camistrate/InkTime_Project/Hardware/schematic.sch

## EAGLE design Hardware/schematic.sch (2026-04-10)

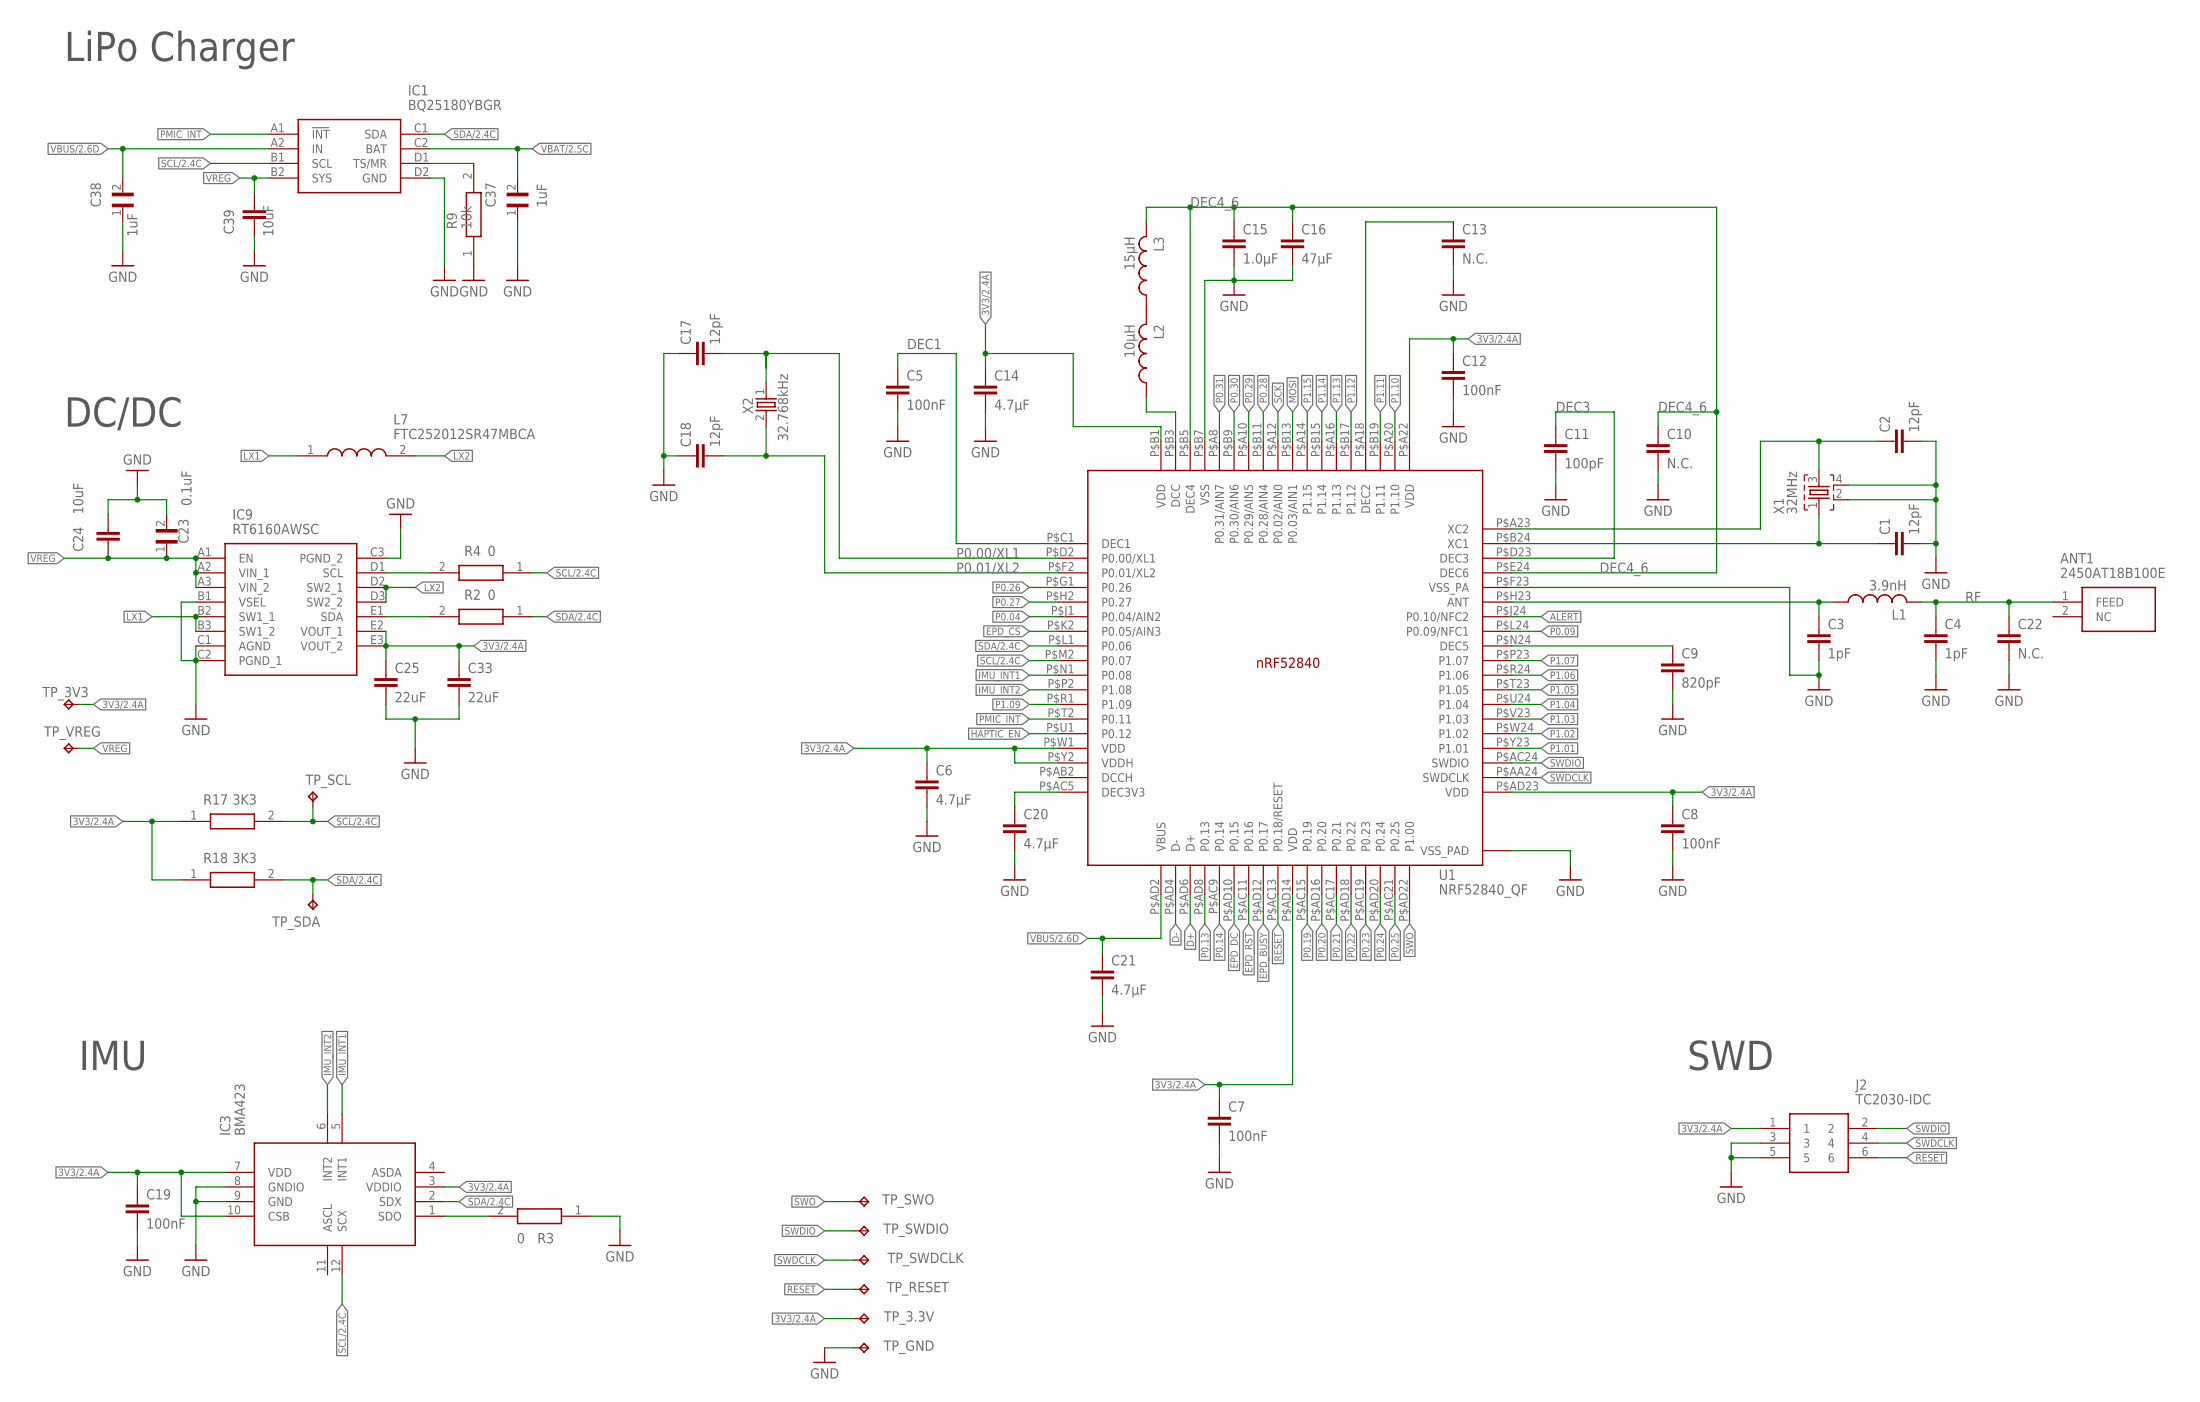
[picture p7: schematic schematic.sch, sheet 1]

Parts:
ANT1: 2450AT18B100E; 2450AT18B100E_ANTC3216X140N
C1, C2, C17, C18: 12pF; NORDIC_NRF_3_RESC0201_L
C3, C4: 1pF; NORDIC_NRF_3_RESC0201_L
C5, C7, C8, C12, C19: 100nF; NORDIC_NRF_3_RESC0201_L
C6, C14, C20, C21: 4.7µF; NORDIC_NRF_3_RESC0402_L
C9: 820pF; NORDIC_NRF_3_RESC0201_L
C10, C13, C22: N.C.; NORDIC_NRF_3_RESC0201_L
C11: 100pF; NORDIC_NRF_3_RESC0201_L
C15: 1.0µF; NORDIC_NRF_3_RESC0402_L
C16: 47µF; NORDIC_NRF_3_RESC0402_L
C23: 0.1uF; GRM011R60J152KE01L_2_CAPC0201X13N
C24, C39: 10uF; NORDIC_NRF_3_RESC0402_L
C25, C33: 22uF; NORDIC_NRF_3_RESC0402_L
C37, C38: 1uF; GRM011R60J152KE01L_2_CAPC0201X13N
IC1: BQ25180YBGR; BQ25180YBGR_BGA8C40P2X4_100X155X50
IC3: BMA423; BMA423_BMA423
IC9: RT6160AWSC; RT6160AWSC_BGA15C40P3X5_140X230X60
J2: TC2030-IDC; TC2030-IDC_TC2030IDC
L1: 3.9nH; NORDIC_NRF_2_RESC0201_N
L2: 10µH; NORDIC_NRF_2_RESC0201_N
L3: 15µH; NORDIC_NRF_2_RESC0201_N
L7: FTC252012SR47MBCA; MLP2016SR47MT0S1_INDC2016X100N
R2, R4: 0; CPF0201D7K68C1_0201
R3: 0; ERA-1AEB3401C_0201
R9: 10k; CPF0201D7K68C1_0201
R17, R18: 3K3; ERA-1AEB3401C_0201
TP_3.3V, TP_3V3: HECTOR_WATCH_1_TPTP20R; HECTOR_WATCH_1_TP20R
TP_GND: HECTOR_WATCH_1_TPTP20R; HECTOR_WATCH_1_TP20R
TP_RESET: HECTOR_WATCH_1_TPTP20R; HECTOR_WATCH_1_TP20R
TP_SCL: HECTOR_WATCH_1_TPTP20R; HECTOR_WATCH_1_TP20R
TP_SDA: HECTOR_WATCH_1_TPTP20R; HECTOR_WATCH_1_TP20R
TP_SWDCLK: HECTOR_WATCH_1_TPTP20R; HECTOR_WATCH_1_TP20R
TP_SWDIO: HECTOR_WATCH_1_TPTP20R; HECTOR_WATCH_1_TP20R
TP_SWO: HECTOR_WATCH_1_TPTP20R; HECTOR_WATCH_1_TP20R
TP_VREG: HECTOR_WATCH_1_TPTP20R; HECTOR_WATCH_1_TP20R
U1: NRF52840_QF; NORDIC_NRF_4_AQFN50P700X700X85_HS-74N
X1: 32MHz; NORDIC_NRF_BT-XTAL_2016_N
X2: 32.768kHz; NORDIC_NRF_1_XTAL_3215_N

Connections:
3V3/2.4A: C6.1, C7.1, C8.1, C12.1, C14.1, C19.1, C25.1, C33.1, IC3.3 (VDDIO), IC3.7 (VDD), IC3.10 (CSB), IC9.E2 (VOUT_1), IC9.E3 (VOUT_2), J2.1, R17.1, R18.1, TP_3.3V.TP, TP_3V3.TP, U1.P$A22 (VDD), U1.P$AD14 (VDD), U1.P$AD23 (VDD), U1.P$B1 (VDD), U1.P$W1 (VDD), U1.P$Y2 (VDDH)
ALERT: U1.P$J24 (P0.10/NFC2)
D+: U1.P$AD6 (D+)
D-: U1.P$AD4 (D-)
DEC1: C5.1, U1.P$C1 (DEC1)
DEC3: C11.1, U1.P$D23 (DEC3)
DEC4_6: C10.1, C15.1, C16.1, L3.2, U1.P$B5 (DEC4), U1.P$E24 (DEC6)
EPD_BUSY: U1.P$AD12 (P0.17)
EPD_CS: U1.P$K2 (P0.05/AIN3)
EPD_DC: U1.P$AD10 (P0.15)
EPD_RST: U1.P$AC11 (P0.16)
GND: C1.2, C2.2, C3.2, C4.2, C5.2, C6.2, C7.2, C8.2, C9.2, C10.2, C11.2, C12.2, C13.2, C14.2, C15.2, C16.2, C17.1, C18.1, C19.2, C20.2, C21.2, C22.2, C23.2, C24.1, C25.2, C33.2, C37.1, C38.1, C39.2, IC1.D2 (GND), IC3.8 (GNDIO), IC3.9 (GND), IC9.B1 (VSEL), IC9.C1 (AGND), IC9.C2 (PGND_1), IC9.C3 (PGND_2), J2.3, J2.5, R3.1, R9.1, TP_GND.TP, U1.P$74 (VSS_PAD), U1.P$B7 (VSS), U1.P$F23 (VSS_PA), X1.2, X1.4
HAPTIC_EN: U1.P$U1 (P0.12)
IMU_INT1: IC3.5 (INT1), U1.P$N1 (P0.08)
IMU_INT2: IC3.6 (INT2), U1.P$P2 (P1.08)
LX1: IC9.B2 (SW1_1), IC9.B3 (SW1_2), L7.1
LX2: IC9.D2 (SW2_1), IC9.D3 (SW2_2), L7.2
MOSI: U1.P$B13 (P0.03/AIN1)
unnamed: IC9.D1 (SCL), R4.2
unnamed: IC1.D1 (TS/MR), R9.2
unnamed: C20.1, U1.P$AC5 (DEC3V3)
unnamed: IC9.E1 (SDA), R2.2
unnamed: IC3.1 (SDO), R3.2
unnamed: L2.1, U1.P$B3 (DCC)
unnamed: L2.2, L3.1
unnamed: C13.1, U1.P$A18 (DEC2)
unnamed: C9.1, U1.P$N24 (DEC5)
unnamed: C2.1, U1.P$A23 (XC2), X1.3
unnamed: C3.1, L1.1, U1.P$H23 (ANT)
unnamed: C1.1, U1.P$B24 (XC1), X1.1
P0.00/XL1: C17.2, U1.P$D2 (P0.00/XL1), X2.1
P0.01/XL2: C18.2, U1.P$F2 (P0.01/XL2), X2.2
P0.04: U1.P$J1 (P0.04/AIN2)
P0.09: U1.P$L24 (P0.09/NFC1)
P0.13: U1.P$AD8 (P0.13)
P0.14: U1.P$AC9 (P0.14)
P0.19: U1.P$AC15 (P0.19)
P0.20: U1.P$AD16 (P0.20)
P0.21: U1.P$AC17 (P0.21)
P0.22: U1.P$AD18 (P0.22)
P0.23: U1.P$AC19 (P0.23)
P0.24: U1.P$AD20 (P0.24)
P0.25: U1.P$AC21 (P0.25)
P0.26: U1.P$G1 (P0.26)
P0.27: U1.P$H2 (P0.27)
P0.28: U1.P$B11 (P0.28/AIN4)
P0.29: U1.P$A10 (P0.29/AIN5)
P0.30: U1.P$B9 (P0.30/AIN6)
P0.31: U1.P$A8 (P0.31/AIN7)
P1.01: U1.P$Y23 (P1.01)
P1.02: U1.P$W24 (P1.02)
P1.03: U1.P$V23 (P1.03)
P1.04: U1.P$U24 (P1.04)
P1.05: U1.P$T23 (P1.05)
P1.06: U1.P$R24 (P1.06)
P1.07: U1.P$P23 (P1.07)
P1.09: U1.P$R1 (P1.09)
P1.10: U1.P$A20 (P1.10)
P1.11: U1.P$B19 (P1.11)
P1.12: U1.P$B17 (P1.12)
P1.13: U1.P$A16 (P1.13)
P1.14: U1.P$B15 (P1.14)
P1.15: U1.P$A14 (P1.15)
PMIC_INT: IC1.A1 (!INT), U1.P$T2 (P0.11)
RESET: J2.6, TP_RESET.TP, U1.P$AC13 (P0.18/RESET)
RF: ANT1.1 (FEED), C4.1, C22.1, L1.2
SCK: U1.P$A12 (P0.02/AIN0)
SCL/2.4C: IC1.B1 (SCL), IC3.12 (SCX), R4.1, R17.2, TP_SCL.TP, U1.P$M2 (P0.07)
SDA/2.4C: IC1.C1 (SDA), IC3.2 (SDX), R2.1, R18.2, TP_SDA.TP, U1.P$L1 (P0.06)
SWDCLK: J2.4, TP_SWDCLK.TP, U1.P$AA24 (SWDCLK)
SWDIO: J2.2, TP_SWDIO.TP, U1.P$AC24 (SWDIO)
SWO: TP_SWO.TP, U1.P$AD22 (P1.00)
VBAT/2.5C: C37.2, IC1.C2 (BAT)
VBUS/2.6D: C21.1, C38.2, IC1.A2 (IN), U1.P$AD2 (VBUS)
VREG: C23.1, C24.2, C39.1, IC1.B2 (SYS), IC9.A1 (EN), IC9.A2 (VIN_1), IC9.A3 (VIN_2), TP_VREG.TP

Notes on the sheet:
LiPo Charger
DC/DC
IMU
SWD

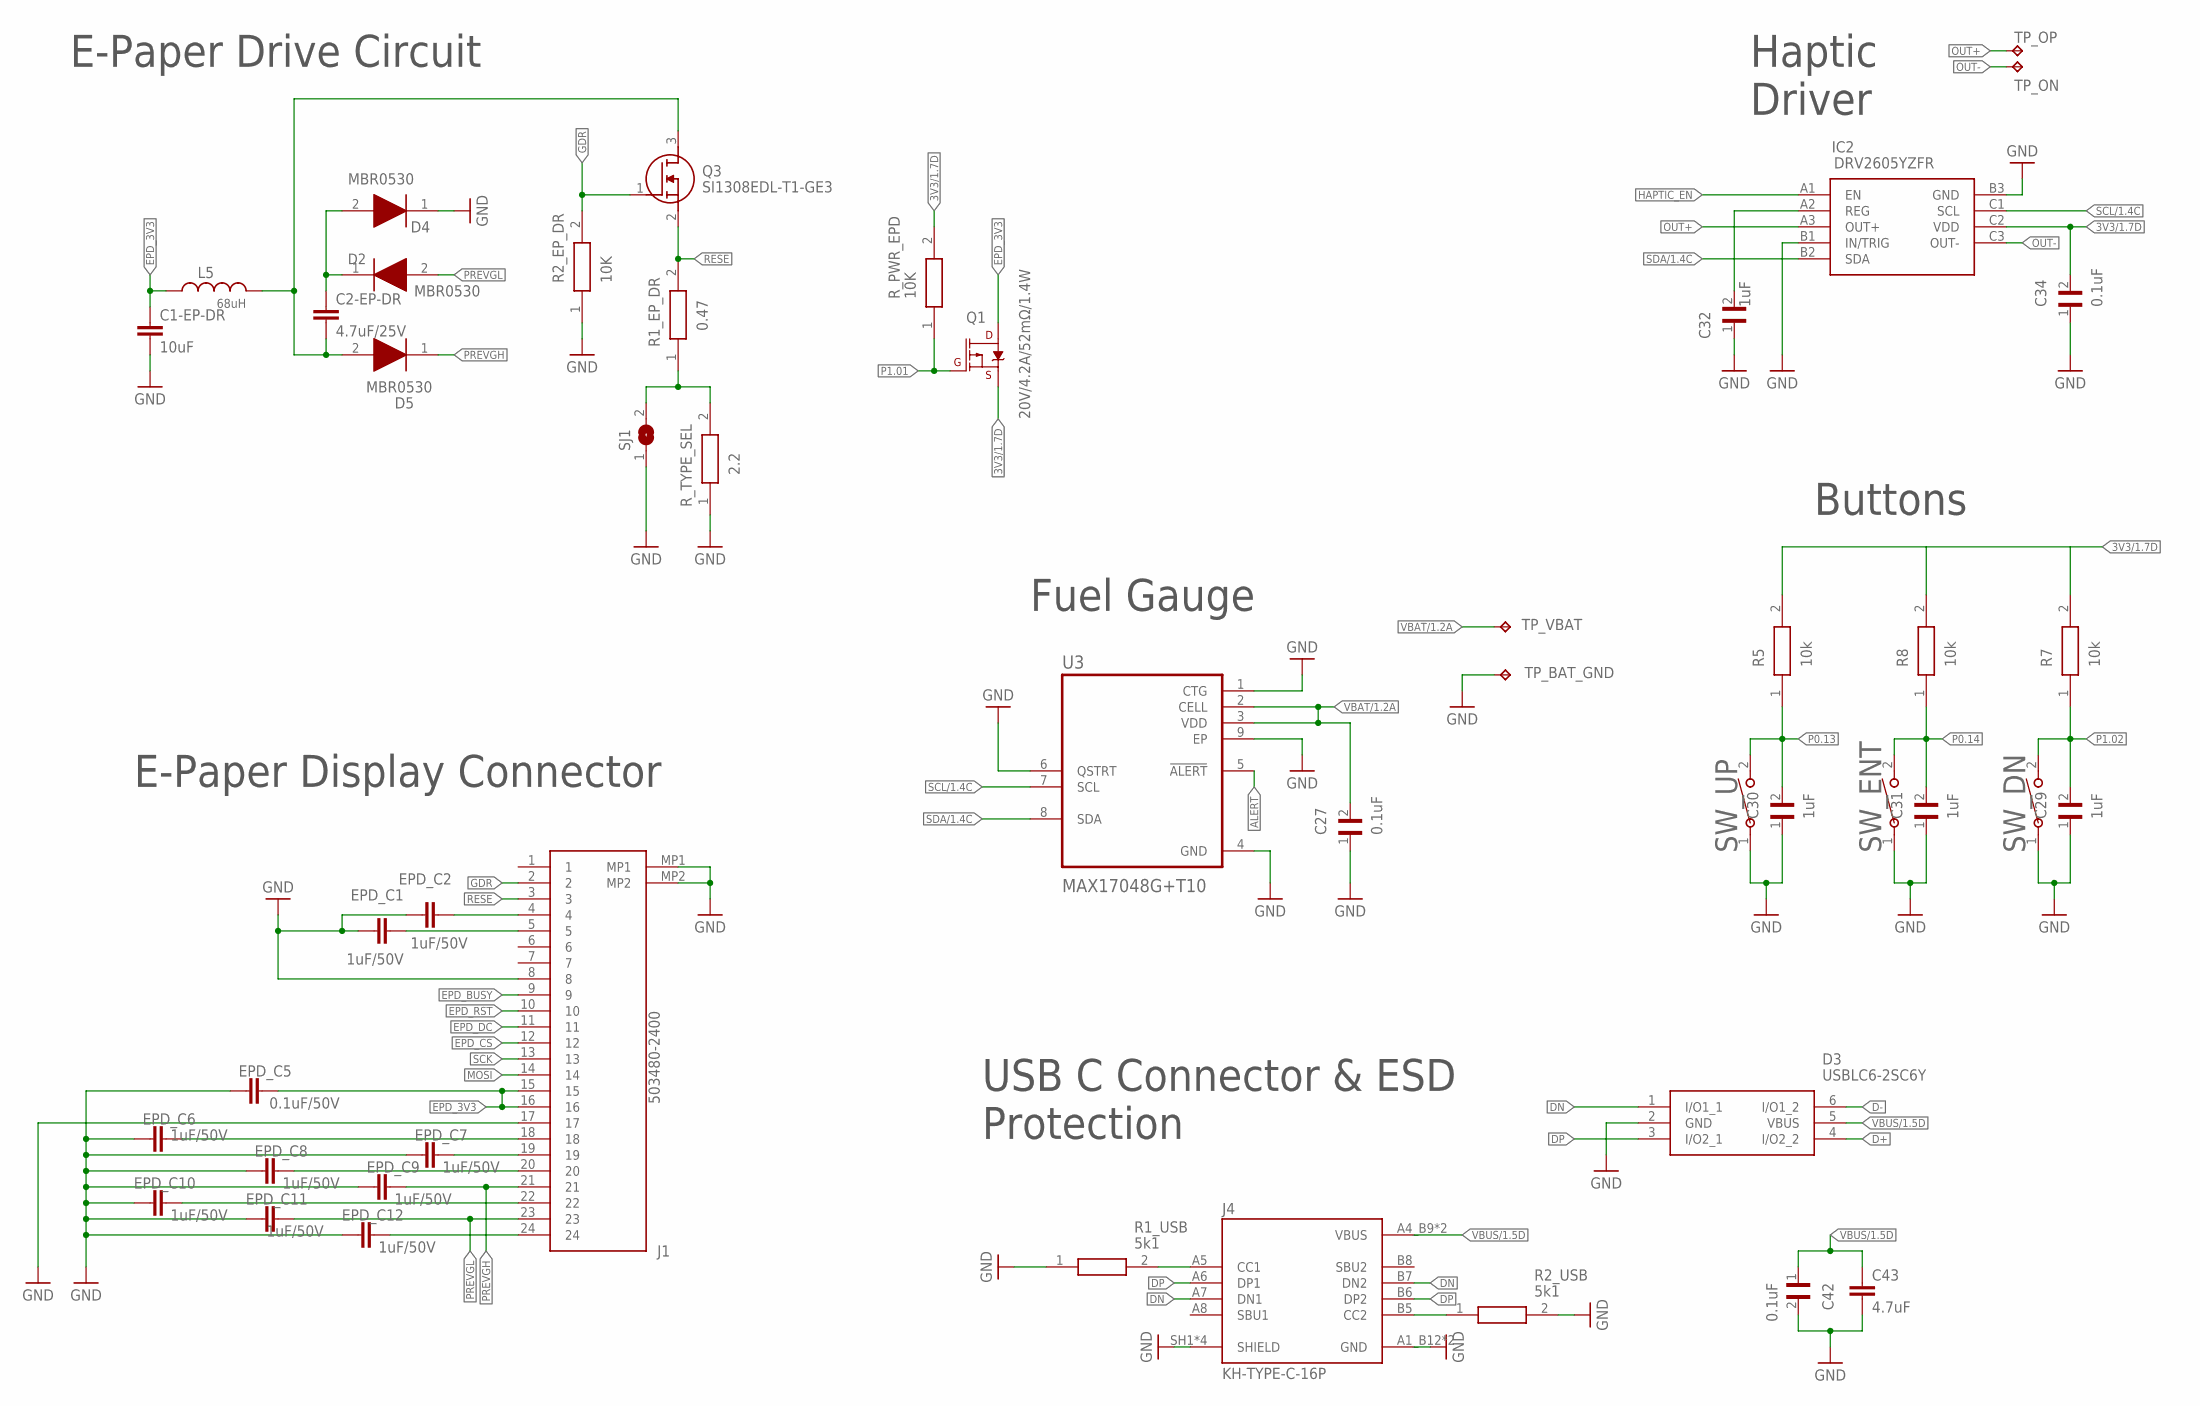
[picture p8: schematic schematic.sch, sheet 2]

Parts:
C1-EP-DR: 10uF; NORDIC_NRF_3_RESC0402_L
C2-EP-DR: 4.7uF/25V; NORDIC_NRF_3_RESC0402_L
C27, C34, C42: 0.1uF; GRM011R60J152KE01L_2_CAPC0201X13N
C29, C30, C31, C32: 1uF; GRM011R60J152KE01L_2_CAPC0201X13N
C43: 4.7uF; NORDIC_NRF_3_RESC0402_L
D2, D4, D5: MBR0530; ESP32_C6_LIBRARY_5_SOD3716X135N
D3: USBLC6-2SC6Y; ESP32_C6_LIBRARY_3_SOT95P280X145-6N
EPD_C1, EPD_C2: 1uF/50V; NORDIC_NRF_3_RESC0201_L
EPD_C5: 0.1uF/50V; NORDIC_NRF_3_RESC0201_L
EPD_C6, EPD_C7, EPD_C8, EPD_C9, EPD_C10, EPD_C11, EPD_C12: 1uF/50V; NORDIC_NRF_3_RESC0402_L
IC2: DRV2605YZFR; DRV2605YZFR_BGA9C50P3X3_144X144X62
J1: 503480-2400; 503480-2400_5034802400
J4: KH-TYPE-C-16P; KH-TYPE-C-16P_KINGHELM_KH-TYPE-C-16P
L5: 68uH; NORDIC_NRF_2_RESC0201_N
Q1: 20V/4.2A/52mΩ/1.4W; ESP32_C6_LIBRARY_4_ESP32_C6_LIBRARY_4_ESP32_C6_LIBRARY_4_ES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
Q3: SI1308EDL-T1-GE3; ESP32_C6_LIBRARY_6_SOT65P210X110-3N
R1_EP_DR: 0.47; CPF0201D7K68C1_0201
R1_USB, R2_USB: 5k1; ERA-1AEB3401C_0201
R2_EP_DR: 10K; CPF0201D7K68C1_0201
R5, R7, R8: 10k; CPF0201D7K68C1_0201
R_PWR_EPD: 10K; CPF0201D7K68C1_0201
R_TYPE_SEL: 2.2; CPF0201D7K68C1_0201
SJ1: ESP32_C6_LIBRARY_7_JUMPER_SJ
SW_DN: 2025-10-22_07-23-44_LIBRARY_EVP-AKE31ASW_EVP-AKE3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; 2025-10-22_07-23-44_LIBRARY_SW_EVP-AKE31A_PAN
SW_ENT: 2025-10-22_07-23-44_LIBRARY_EVP-AKE31ASW_EVP-AKE3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; 2025-10-22_07-23-44_LIBRARY_SW_EVP-AKE31A_PAN
SW_UP: 2025-10-22_07-23-44_LIBRARY_EVP-AKE31ASW_EVP-AKE3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; 2025-10-22_07-23-44_LIBRARY_SW_EVP-AKE31A_PAN
TP_BAT_GND: HECTOR_WATCH_1_TPTP20R; HECTOR_WATCH_1_TP20R
TP_ON: HECTOR_WATCH_1_TPTP20R; HECTOR_WATCH_1_TP20R
TP_OP: HECTOR_WATCH_1_TPTP20R; HECTOR_WATCH_1_TP20R
TP_VBAT: HECTOR_WATCH_1_TPTP20R; HECTOR_WATCH_1_TP20R
U3: MAX17048G+T10; ESP32_C6_LIBRARY_SON50P200X200X80-9N

Connections:
3V3/1.7D: C34.2, IC2.C2 (VDD), Q1.2 (S), R5.2, R_PWR_EPD.2
ALERT: U3.5 (!ALERT)
D+: D3.4 (I/O2_2)
D-: D3.6 (I/O1_2)
DN: D3.1 (I/O1_1), J4.A7 (DN1), J4.B7 (DN2)
DP: D3.3 (I/O2_1), J4.A6 (DP1), J4.B6 (DP2)
EPD_3V3: C1-EP-DR.1, EPD_C5.2, J1.15, J1.16, L5.1, Q1.3 (D)
EPD_BUSY: J1.9
EPD_CS: J1.12
EPD_DC: J1.11
EPD_RST: J1.10
GDR: J1.2, Q3.1 (G), R2_EP_DR.2
GND: C1-EP-DR.2, C27.1, C29.1, C30.1, C31.1, C32.1, C34.1, C42.2, C43.2, D3.2 (GND), D4.1 (K), EPD_C1.1, EPD_C2.1, EPD_C5.1, EPD_C6.1, EPD_C7.1, EPD_C8.1, EPD_C9.1, EPD_C10.1, EPD_C11.1, EPD_C12.1, IC2.B1 (IN/TRIG), IC2.B3 (GND), J1.8, J1.17, J1.MP1, J1.MP2, J4.A1_B12 (GND), J4.SH1 (SHIELD), R1_USB.1, R2_EP_DR.1, R2_USB.2, R_TYPE_SEL.1, SJ1.1, SW_DN.1, SW_ENT.1, SW_UP.1, TP_BAT_GND.TP, U3.1 (CTG), U3.4 (GND), U3.6 (QSTRT), U3.9 (EP)
HAPTIC_EN: IC2.A1 (EN)
MOSI: J1.14
unnamed: EPD_C7.2, J1.19
unnamed: C2-EP-DR.1, D2.1 (K), D4.2 (A)
unnamed: C2-EP-DR.2, D5.2 (A), L5.2, Q3.3 (D)
unnamed: R1_EP_DR.1, R_TYPE_SEL.2, SJ1.2
unnamed: EPD_C2.2, J1.4
unnamed: EPD_C1.2, J1.5
unnamed: EPD_C12.2, J1.24
unnamed: EPD_C8.2, J1.20
unnamed: EPD_C10.2, J1.22
unnamed: EPD_C6.2, J1.18
unnamed: C32.2, IC2.A2 (REG)
unnamed: J4.B5 (CC2), R2_USB.1
unnamed: J4.A5 (CC1), R1_USB.2
OUT+: IC2.A3 (OUT+), TP_OP.TP
OUT-: IC2.C3 (OUT-), TP_ON.TP
P0.13: C30.2, R5.1, SW_UP.2
P0.14: C31.2, R8.1, SW_ENT.2
P1.01: Q1.1 (G), R_PWR_EPD.1
P1.02: C29.2, R7.1, SW_DN.2
PREVGH: D5.1 (K), EPD_C9.2, J1.21
PREVGL: D2.2 (A), EPD_C11.2, J1.23
RESE: J1.3, Q3.2 (S), R1_EP_DR.2
SCK: J1.13
SCL/1.4C: IC2.C1 (SCL), U3.7 (SCL)
SDA/1.4C: IC2.B2 (SDA), U3.8 (SDA)
VBAT/1.2A: C27.2, TP_VBAT.TP, U3.2 (CELL), U3.3 (VDD)
VBUS/1.5D: C42.1, C43.1, D3.5 (VBUS), J4.A4_B9 (VBUS)

Notes on the sheet:
E-Paper Drive Circuit
E-Paper Display Connector
Fuel Gauge
Haptic Driver
Buttons
USB C Connector & ESD Protection
